SolderedElectronics/Breadboard-power-supply-board-hardware-design/OUTPUTS/v1.3/Breadboard power supply board Pinout.png

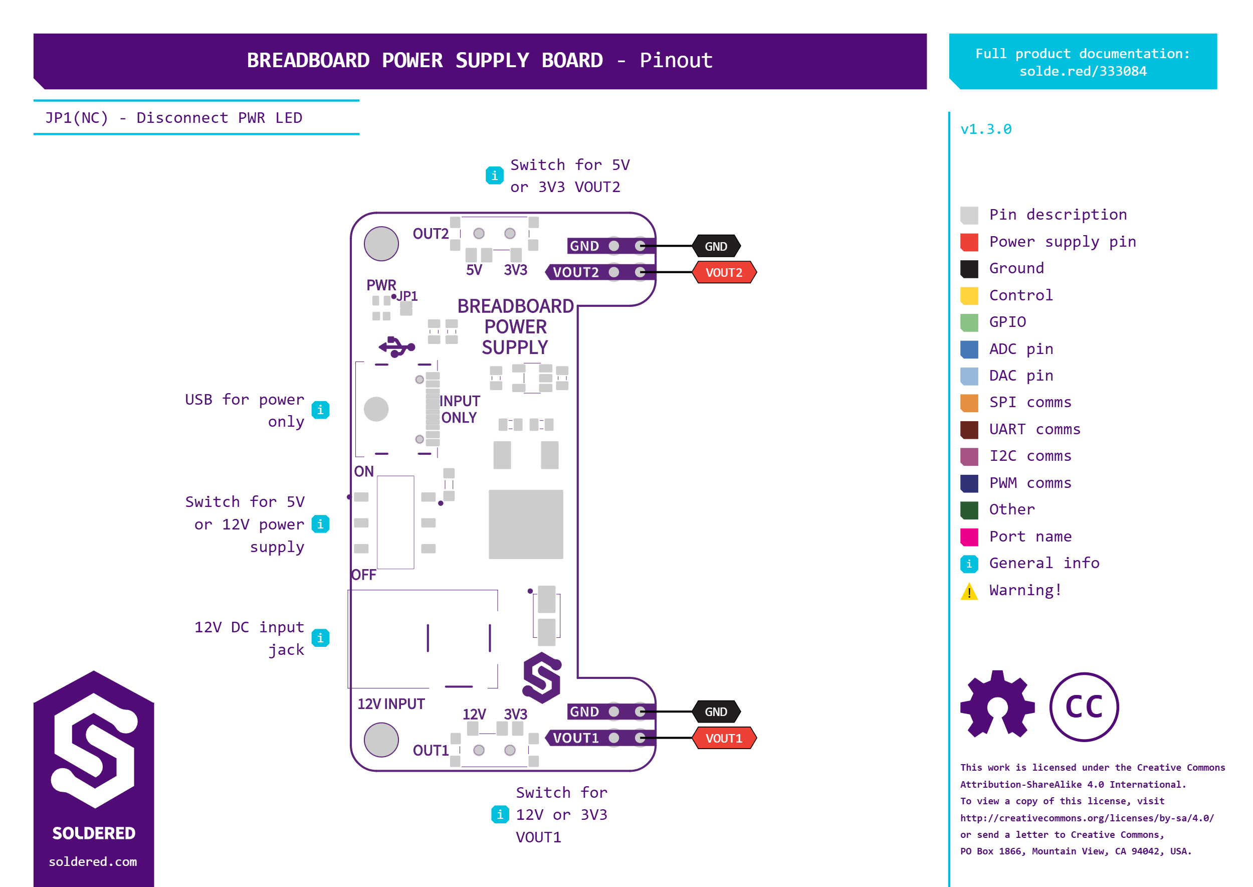
OUTPUTS/v1.3/Breadboard power supply board Pinout.png
